FrankBrigk/mpcnc/Druckdateien/STLs/Wire_Darryl.STL

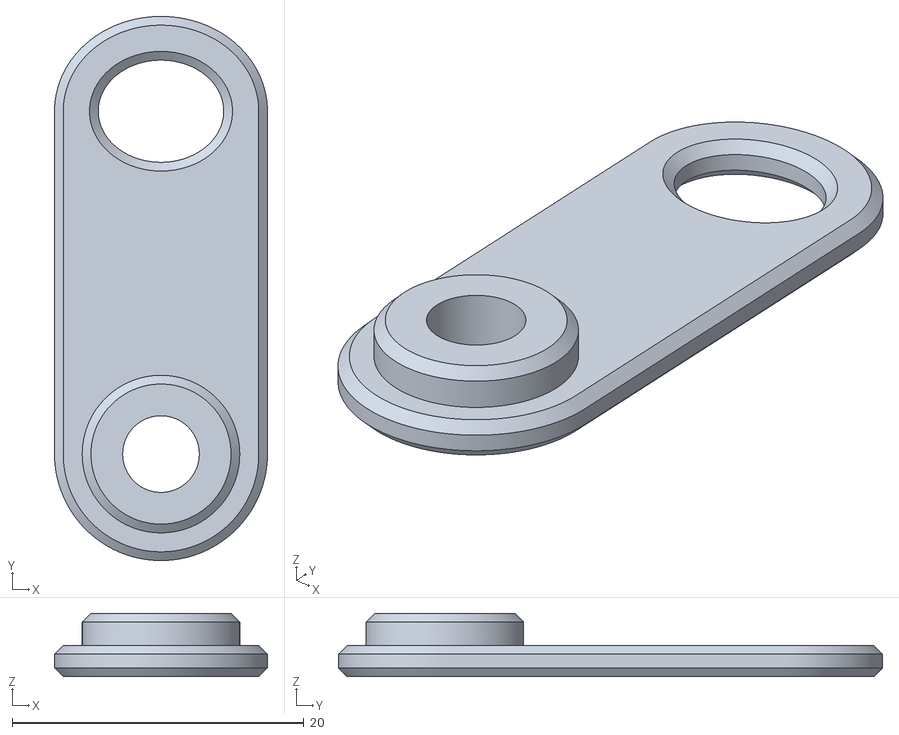
[picture p17: CAD file, 2022-01-13]
Druckdateien/STLs/Wire_Darryl.STL
14.6 x 37.3 x 4.35
