FrankBrigk/mpcnc/Druckdateien/STLs/Lower_Tool_Plate_F_Primo.STL

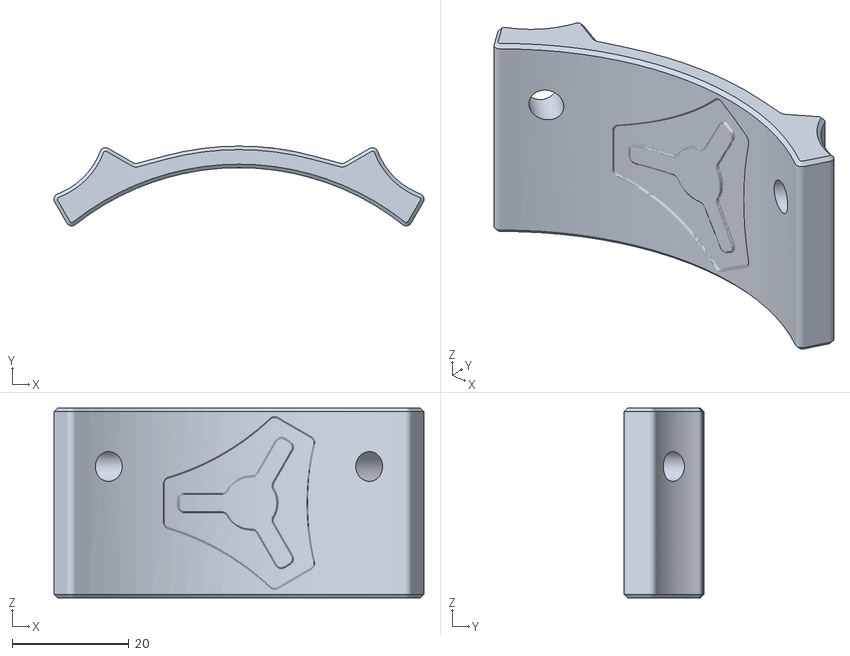
[picture p18: CAD file, 2022-01-13]
Druckdateien/STLs/Lower_Tool_Plate_F_Primo.STL
63.3 x 13.7 x 32.5
