FrankBrigk/mpcnc/Druckdateien/STLs/Upper_Tool_Plate_F_Primo.STL

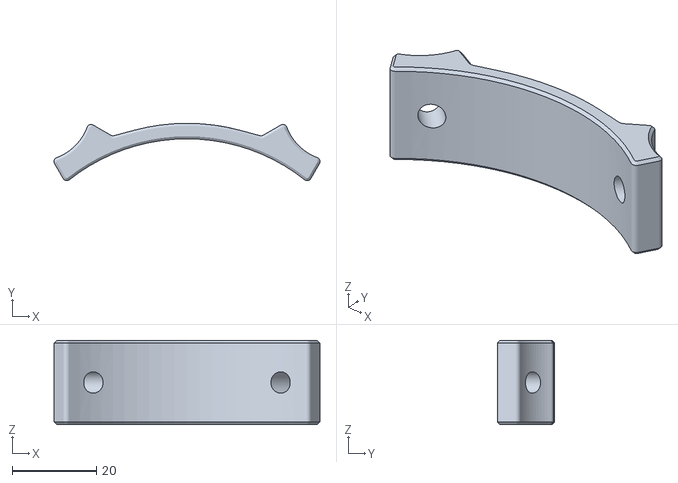
[picture p19: CAD file, 2022-01-13]
Druckdateien/STLs/Upper_Tool_Plate_F_Primo.STL
63.3 x 13.7 x 20.0
