FrankBrigk/mpcnc/Druckdateien/STLs/Z_Coupler_F_Primo.STL

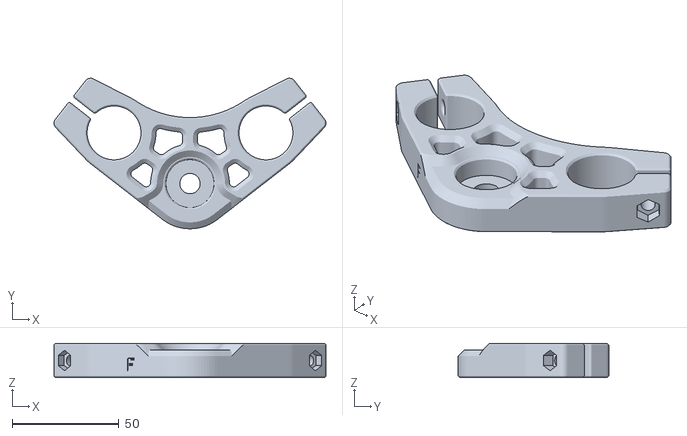
[picture p20: CAD file, 2022-01-13]
Druckdateien/STLs/Z_Coupler_F_Primo.STL
127.3 x 70.4 x 16.0
